andres-garcia-alves/electronics-ardutester/Documentation/ArduTester v1.13k Docs.pdf

? =

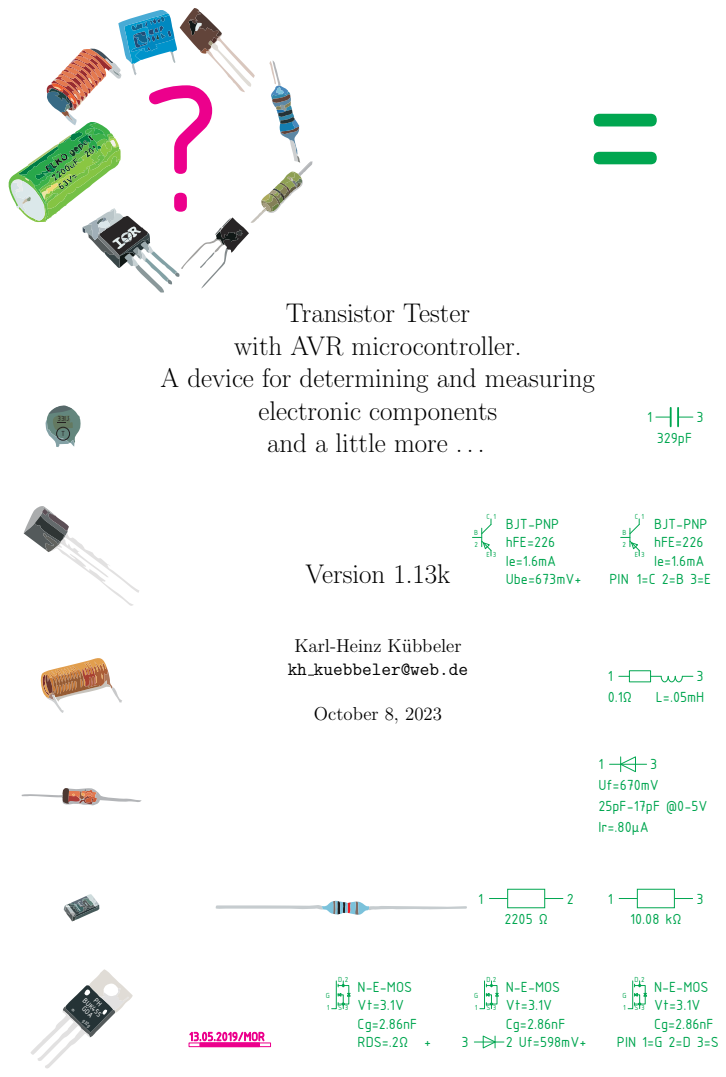
[picture p132: page 1]
13.05.2019/MOR; N-E-MOS Vt=3.1V Cg=2.86nF; RDS=.2; BJT-PNP hFE=226 Ie=1.6mA Ube=673mV+; BJT-PNP hFE=226 Ie=1.6mA PIN 1=C 2=B 3=E; N-E-MOS Vt=3.1V Cg=2.86nF PIN 1=G 2=D 3=S; S3 BUK455; PH GOA; Version 1.13k; October 8, 2023

Transistor Tester
with AVR microcontroller.

A device for determining and measuring

electronic components
and a little more . . .

Karl-Heinz K¨ubbeler
kh kuebbeler@web.de

# Contents

1 Features | 5
2 Hardware | 9
3 Instructions for use | 37
4 Programming of the TransistorTester | 46

5 Description of the measurement procedures | 69
5.3.4 | Measurement of very small capacity values with the sampling technique . . . . 95
6 Signal generation | 135
7 Known errors and unsolved problems | 136
8 Special Software Parts | 138
9 To Do List and new ideas | 139

## Preface

### Basic Motive

Every hobbyist knows the following problem: You remove a transistor from a printed circuit board (PCB) or you get one out of a collection box. If you find out the identification number and you already have a data sheet or you can get the documents about this part, everything is well. But if you don’t find any documents, you have no idea what kind of part this could be. With the conventional approach of measurement it is difficult and time-consuming to find out the type of the part and its parameters. It could be a NPN, PNP, N- or P-channel MOSFET, etc. It was the idea of Markus F. to hand over the work to an AVR microcontroller.

### How my work started

My work with the software of the TransistorTester of Markus F. [2] started because I had problems with my programmer. I had bought a PCB and components, but I could not program the EEprom of the ATmega8 using the Windows driver without error messages. Therefore I took the software of Markus F. and changed all the accesses from the EEprom memory to flash memory accesses. By analysing the software in order to save memory at other places of program, I had the idea, to change the result of the ReadADC function from ADC units to millivolt (mV) units. The mV units are needed for any output of voltage values. If ReadADC returns the value in mV, I can avoid unneces-sary repeated conversion of returned value. To obtain the ADC value in mV, we first accumulate the sum of 22 ADC readings. The sum is multiplied by two and divided by nine. That gives a maximum value of 1023·22·2
9 = 5001, which matches perfectly the desired mV scale of measured voltage values. So I additionally had the hope that the enhancement of ADC resolution by oversampling could help to improve the voltage reading of the ADC, as described in AVR121 [7]. The original version ReadADC accumulated the result of 20 ADC measurements and divided afterwards by 20, so the result is equal to original ADC resolution. This was suboptimal because it missed an opportunity to enhance the ADC’s resolution. Changing ReadADC was a small amount of work, but this forced analysing the whole program and changing all conditional statements in the program where voltage values are queried. But this was only the beginning of my work!
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
