andres-garcia-alves/electronics-ardutester/Documentation/ArduTester Wiki.pdf

Willkommen in der Mikrocontroller.net Artikelsammlung. Alle Artikel hier können nach dem Wiki-Prinzip von jedem bearbeitet werden. Zur Hauptseite der Artikelsammlung

## AVR Transistortester

Aus der Mikrocontroller.net Artikelsammlung, mit Beiträgen verschiedener Autoren (siehe Versionsgeschichte)

Inhaltsverzeichnis

1 Einleitung (deutsch) 2 Introduction (English) 3 Introduktion (dansk) 4 Introduction (Français) 5 Software (deutsch) 6 Software (english) 7 Software (Français) 8 Hardware (deutsch) 9 Hardware (English) 10 Hardware (Français) 11 Downloads (deutsch) 12 Downloads (russisch) - Загрузки (русский) 13 Downloads (English) 14 Downloads (Français) 15 Downloads (Português - Brasil) 16
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
